ashwinnishad98/sysarch/kicad/SensingDeviceSchematics/MPU6050/Adafruit MPU6050.sch

## EAGLE design kicad/SensingDeviceSchematics/MPU6050/Adafruit MPU6050.sch (2024-01-25)

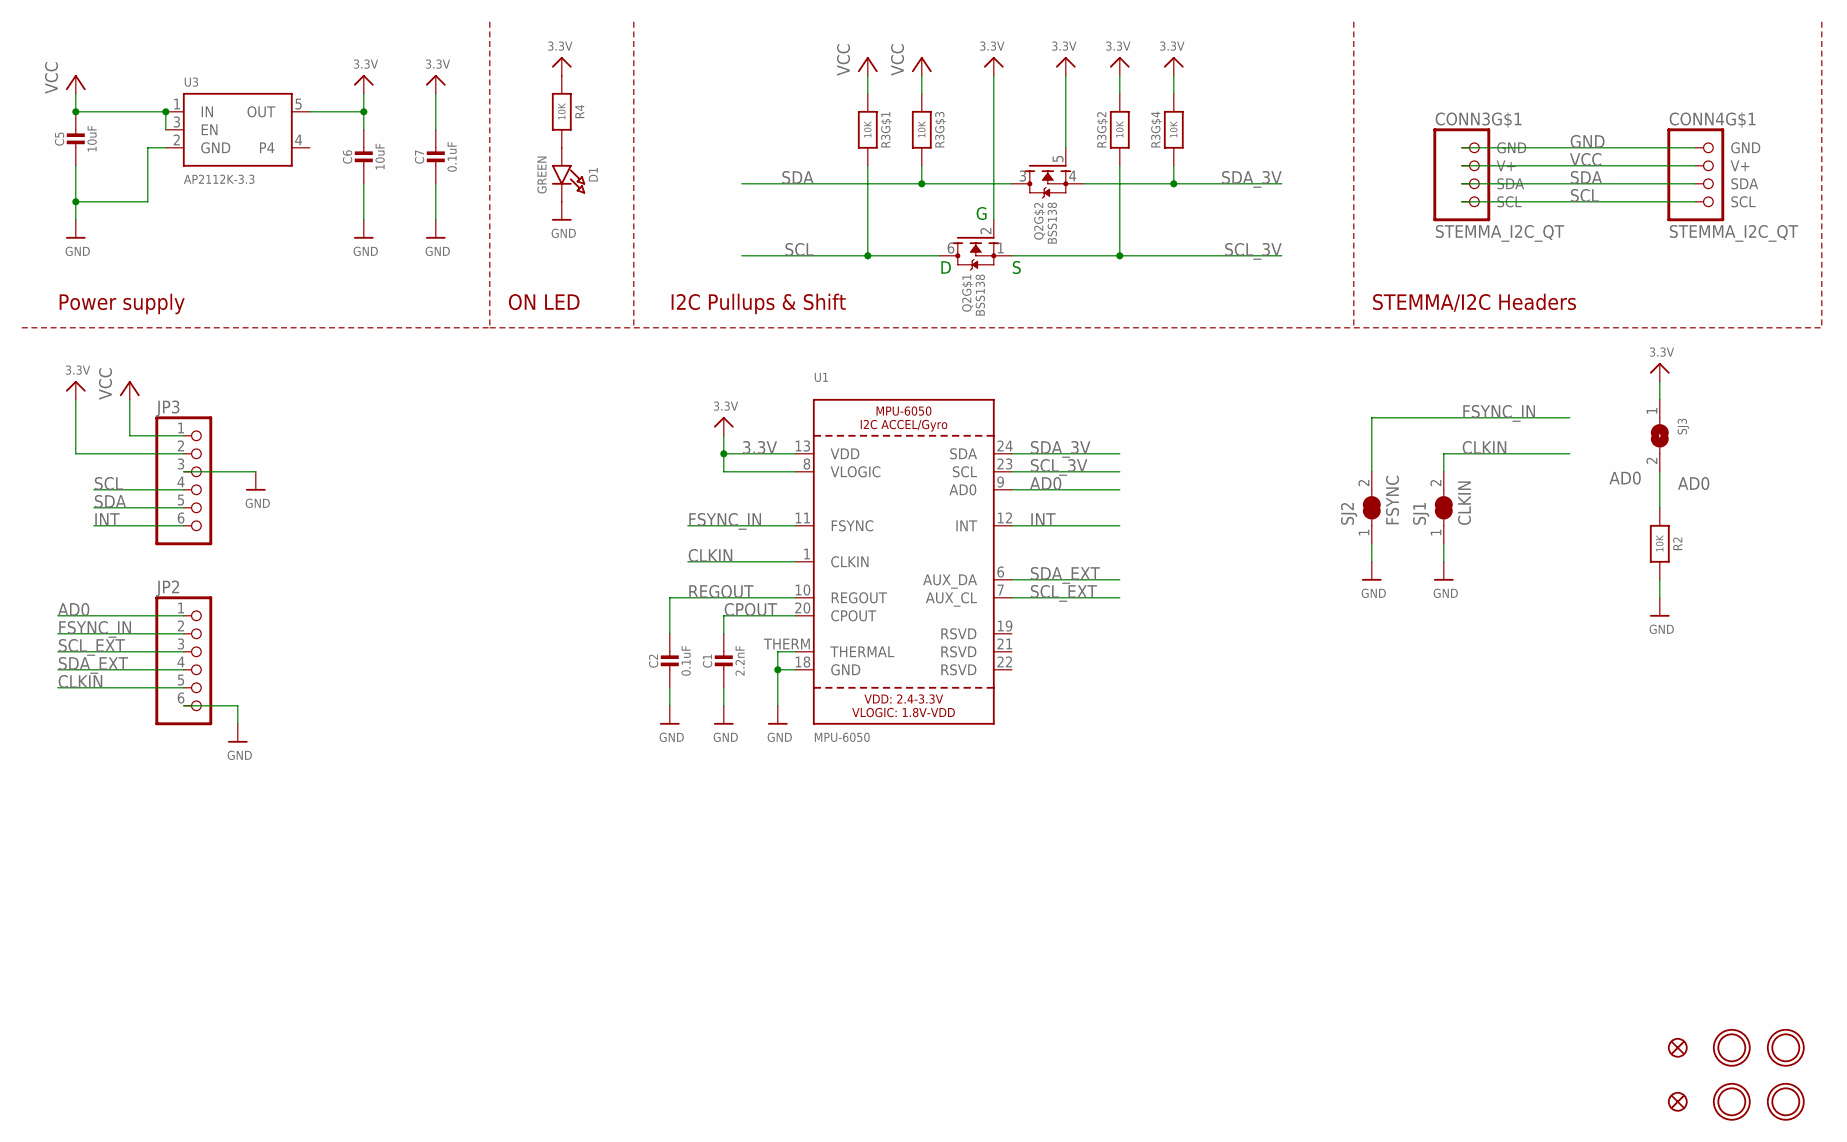
[picture p22: schematic Adafruit MPU6050.sch]

Parts:
C1: 2.2nF; 0603-NO
C2, C7: 0.1uF; 0603-NO
C5, C6: 10uF; 0805-NO
CONN3, CONN4: STEMMA_I2C_QT; JST_SH4
D1: GREEN; CHIPLED_0603_NOOUTLINE
FID3, FID4: FIDUCIAL_1MM
JP2: HEADER-1X6ROUND; 1X06_ROUND
JP3: HEADER-1X670MIL; 1X06_ROUND_70
Q2: BSS138; SOT363
R2, R4: 10K; 0603-NO
R3: 10K; RESPACK_4X0603
SJ1: CLKIN; SOLDERJUMPER_CLOSEDWIRE
SJ2: FSYNC; SOLDERJUMPER_CLOSEDWIRE
SJ3: SOLDERJUMPER; SOLDERJUMPER_ARROW_NOPASTE
U1: MPU-6050; QFN24_4MM_SMSC
U3: AP2112K-3.3; SOT23-5
U$39, U$40, U$42, U$43: MOUNTINGHOLE2.5; MOUNTINGHOLE_2.5_PLATED

Connections:
3.3V: C6.1, C7.1, JP3.2, Q2.2 (G), Q2.5 (G), R3.2 (1), R3.4 (1), R4.1, SJ3.1, U1.8 (VLOGIC), U1.13 (VDD), U3.5 (OUT)
AD0: JP2.1, R2.1, SJ3.2, U1.9 (AD0)
CLKIN: JP2.5, SJ1.2, U1.1 (CLKIN)
CPOUT: C1.1, U1.20 (CPOUT)
FSYNC_IN: JP2.2, SJ2.2, U1.11 (FSYNC)
GND: C1.2, C2.2, C5.2, C6.2, C7.2, CONN3.1 (GND), CONN4.1 (GND), D1.C, JP2.6, JP3.3, R2.2, SJ1.1, SJ2.1, U1.18 (GND), U1.THERM (THERMAL), U3.2 (GND)
INT: JP3.6, U1.12 (INT)
unnamed: D1.A, R4.2
REGOUT: C2.1, U1.10 (REGOUT)
SCL: CONN3.4 (SCL), CONN4.4 (SCL), JP3.4, Q2.6 (D), R3.8 (2)
SCL_3V: Q2.1 (S), R3.7 (2), U1.23 (SCL)
SCL_EXT: JP2.3, U1.7 (AUX_CL)
SDA: CONN3.3 (SDA), CONN4.3 (SDA), JP3.5, Q2.3 (D), R3.6 (2)
SDA_3V: Q2.4 (S), R3.5 (2), U1.24 (SDA)
SDA_EXT: JP2.4, U1.6 (AUX_DA)
VCC: C5.1, CONN3.2 (V+), CONN4.2 (V+), JP3.1, R3.1, R3.3 (1), U3.1 (IN), U3.3 (EN)

Notes on the sheet:
I2C Pullups & Shift
STEMMA/I2C Headers
ON LED
Power supply
