ashwinnishad98/sysarch/kicad/SensingDeviceSchematics/Mic/Adafruit I2S Mic SPK0415HM4H.sch

## EAGLE design kicad/SensingDeviceSchematics/Mic/Adafruit I2S Mic SPK0415HM4H.sch (2024-01-25)

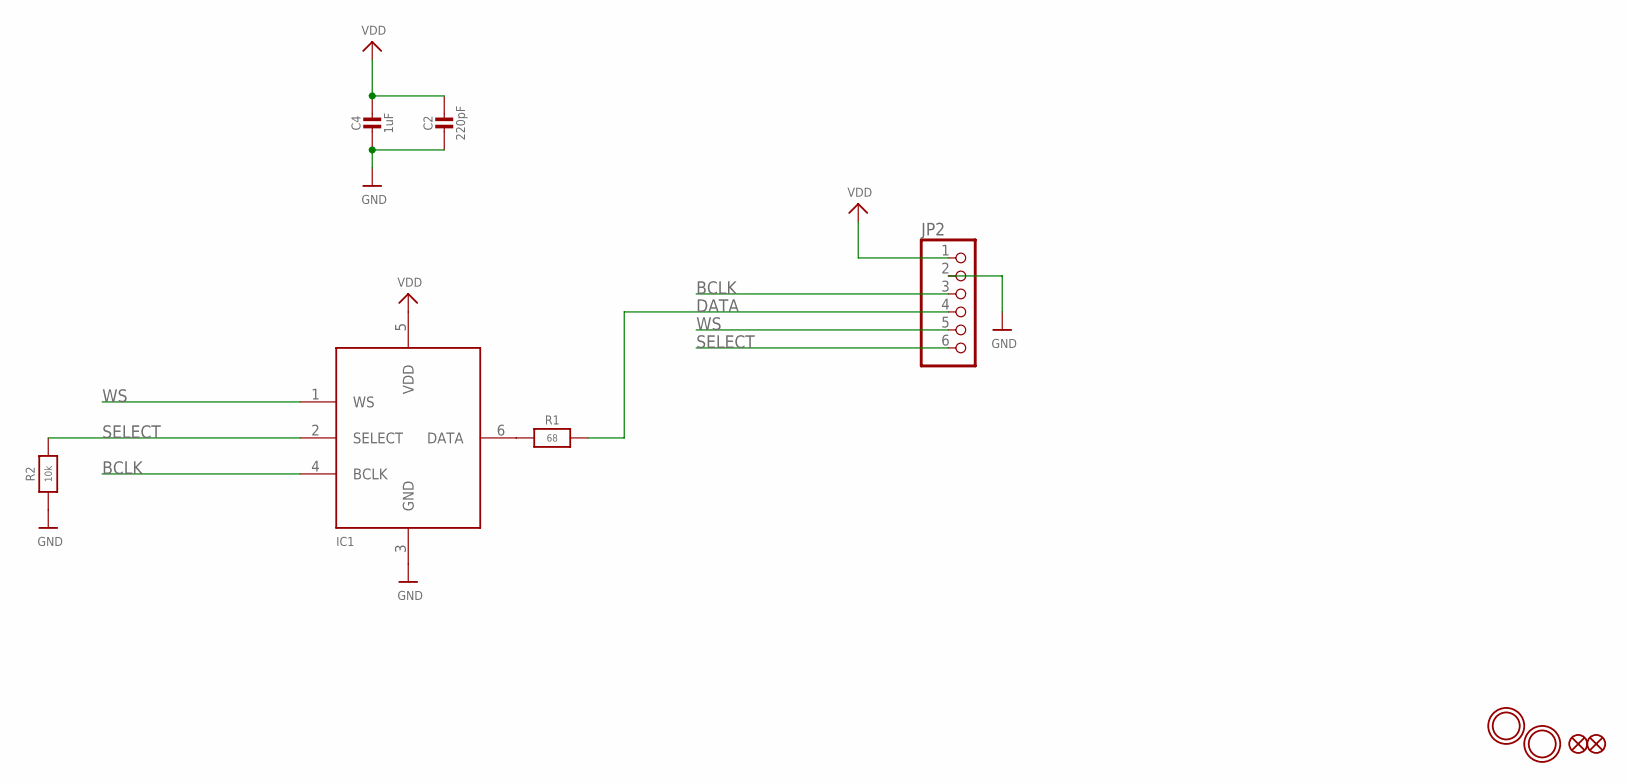
[picture p23: schematic Adafruit I2S Mic SPK0415HM4H.sch]

Parts:
C2: 220pF; 0805-NO
C4: 1uF; 0805-NO
FID1, FID2: FIDUCIAL_1MM
IC1: MIC_I2S_SPH0645; SPH0645LM4H
JP2: HEADER-1X6ROUND; 1X06_ROUND
R1: 68; 0603-NO
R2: 10k; 0603-NO
U$6, U$12: MOUNTINGHOLE2.5; MOUNTINGHOLE_2.5_PLATED

Connections:
BCLK: IC1.4 (BCLK), JP2.3
DATA: JP2.4, R1.2
GND: C2.2, C4.2, IC1.3 (GND), JP2.2, R2.1
unnamed: IC1.6 (DATA), R1.1
SELECT: IC1.2 (SELECT), JP2.6, R2.2
VDD: C2.1, C4.1, IC1.5 (VDD), JP2.1
WS: IC1.1 (WS), JP2.5
